ellak-monades-aristeias/OpenCorner-Space/3D renders_/draft_D_0001.jpg

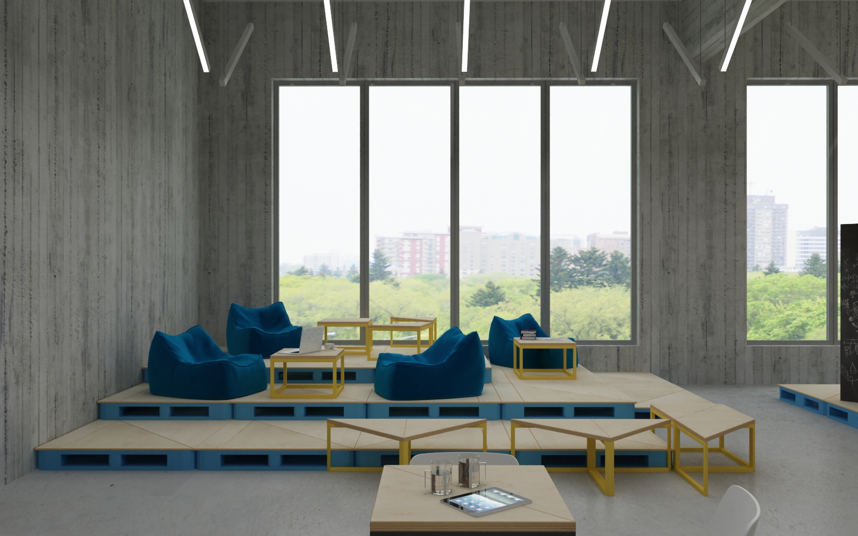
3D renders_/draft_D_0001.jpg
