ellak-monades-aristeias/OpenCorner-Space/3D renders_/draft_D_0009.jpg

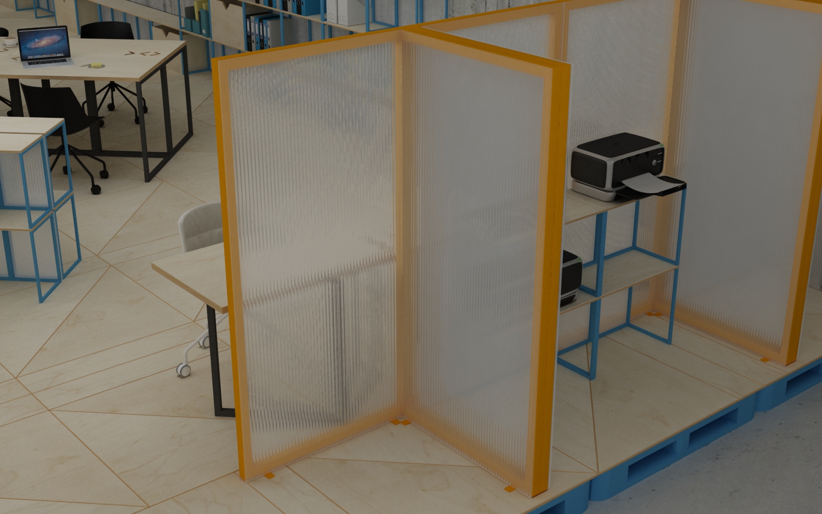
3D renders_/draft_D_0009.jpg
